shawnJxy/multi-room-temp-humidity-monitor-and-control/1.Doc/diagrams/flowchart/system_block.png

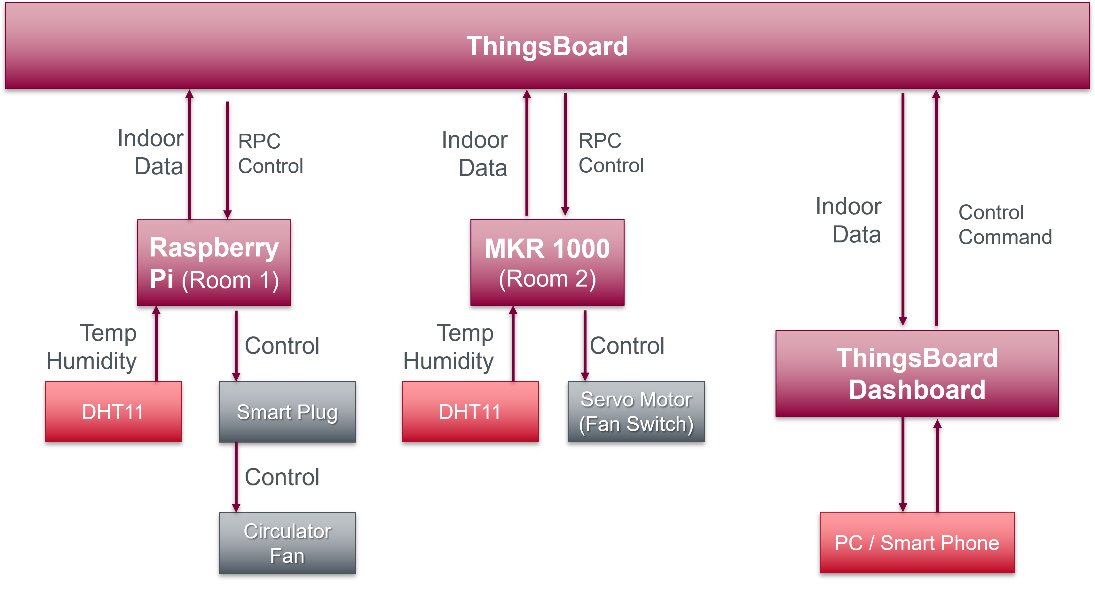
1.Doc/diagrams/flowchart/system_block.png
