shawnJxy/multi-room-temp-humidity-monitor-and-control/2.Code/2.1_Pi_python/dht.py

import time
import sys
import board
import adafruit_dht
import psutil
# We first check if a libgpiod process is running. If yes, we kill it!
for proc in psutil.process_iter():
    if proc.name() == 'libgpiod_pulsein' or proc.name() == 'libgpiod_pulsei':
        proc.kill()

sensor = adafruit_dht.DHT11(board.D4)

def getdata():
    while True:
        try:
            temp = sensor.temperature
            humidity = sensor.humidity
            # print("Temperature: {}*C   Humidity: {}% ".format(temp, humidity))
            return temp,humidity
        except RuntimeError as error:
            print(error.args[0])
            time.sleep(2.0)
            continue
        except Exception as error:
            sensor.exit()
            raise error
            time.sleep(2.0)
